kholia/Simple-TR-Switch/dual-channel-relay-2.jpg

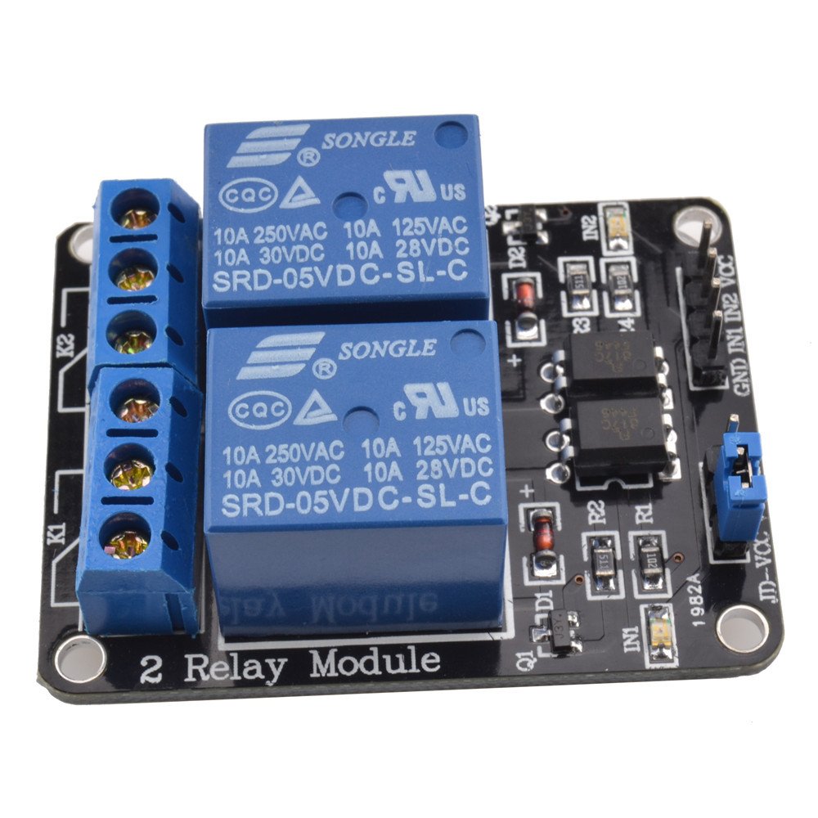
dual-channel-relay-2.jpg
