kholia/Simple-TR-Switch/Extender-PCB-1.png

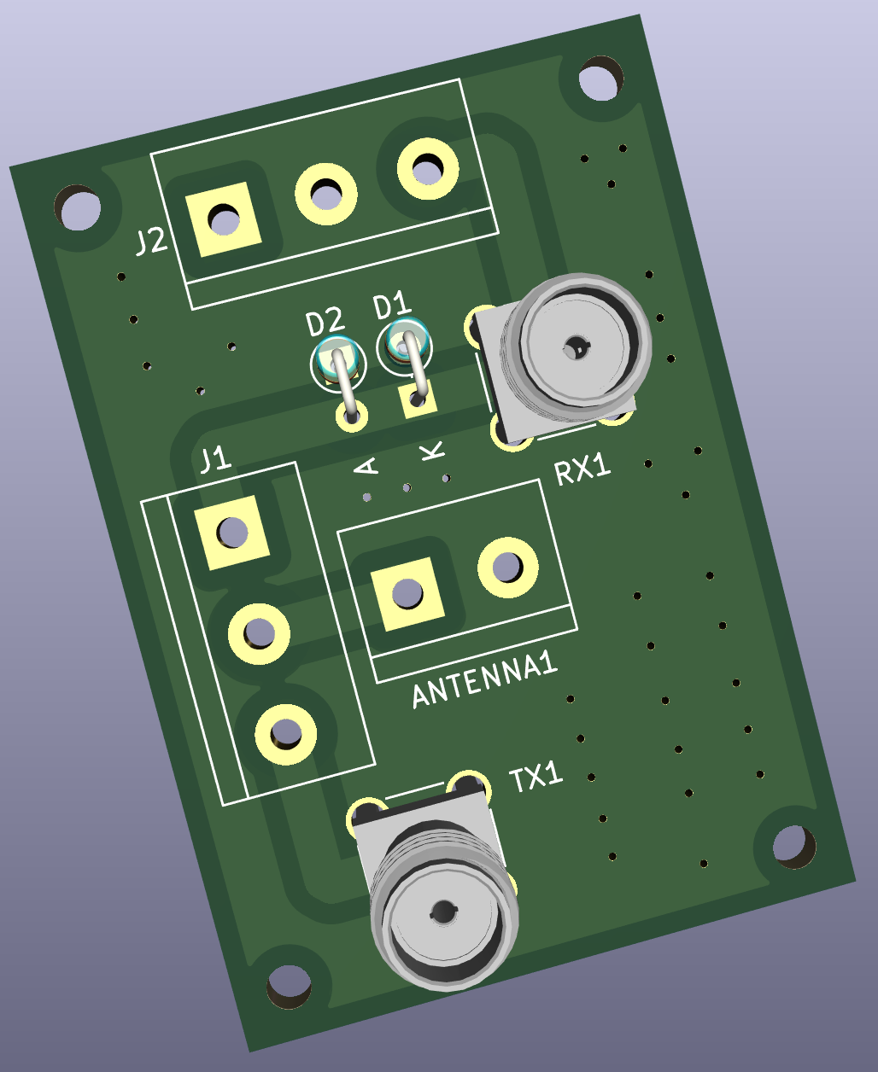
Extender-PCB-1.png
