kholia/Simple-TR-Switch/info/Optocoupler + NPN.png

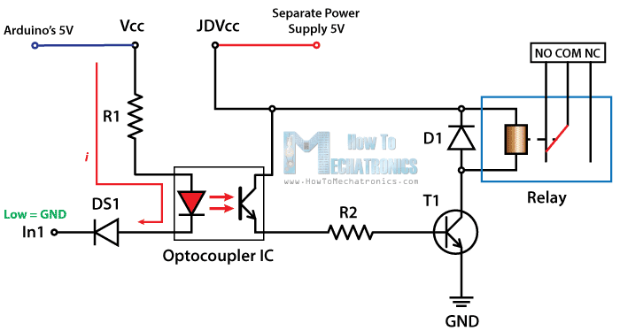
info/Optocoupler + NPN.png
