kholia/Simple-TR-Switch/info/Optocoupler-Relay-Driver-with-PC817-2N3904.jpg

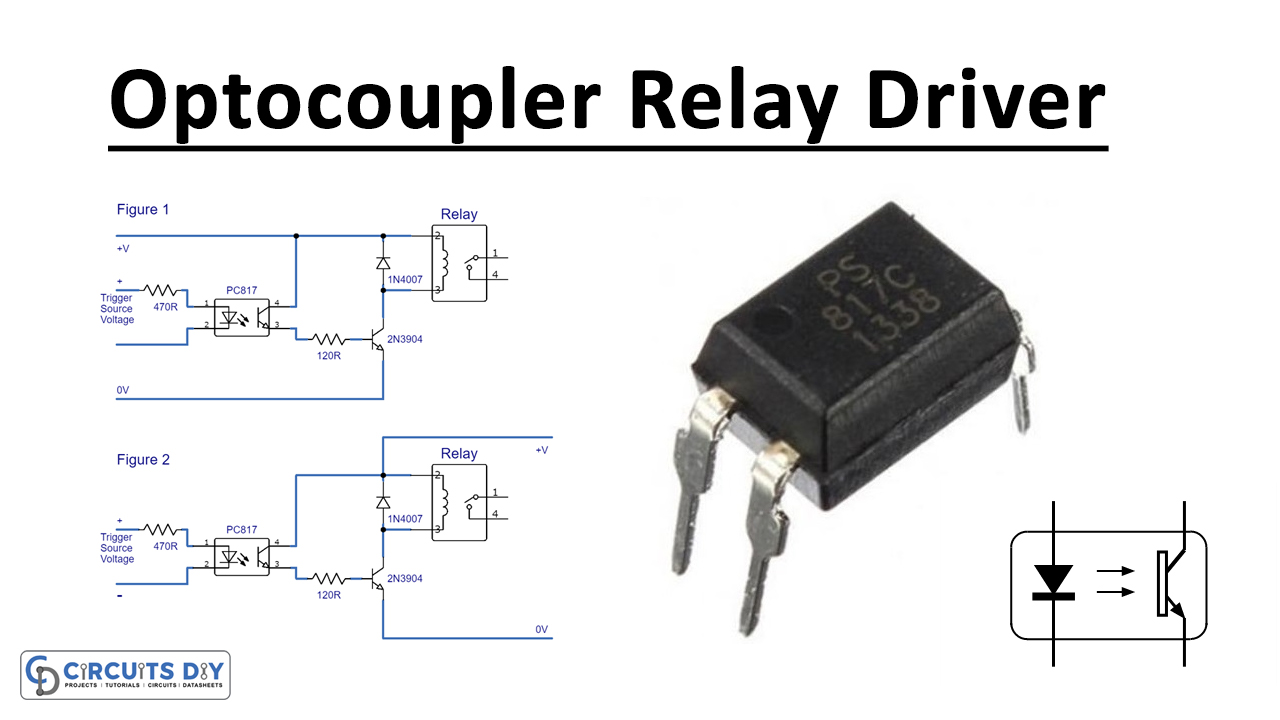
info/Optocoupler-Relay-Driver-with-PC817-2N3904.jpg
