kholia/Simple-TR-Switch/info/Optocoupler-With-Relay.png

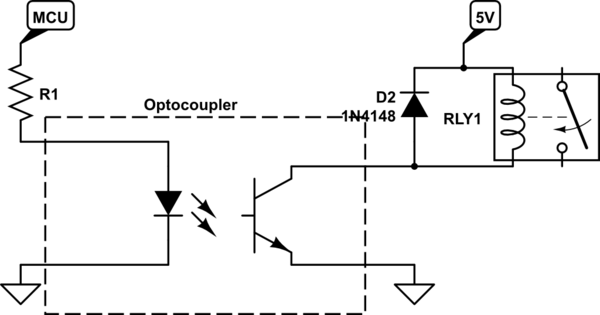
info/Optocoupler-With-Relay.png
