kholia/Simple-TR-Switch/PCB-Rendering-v3.png

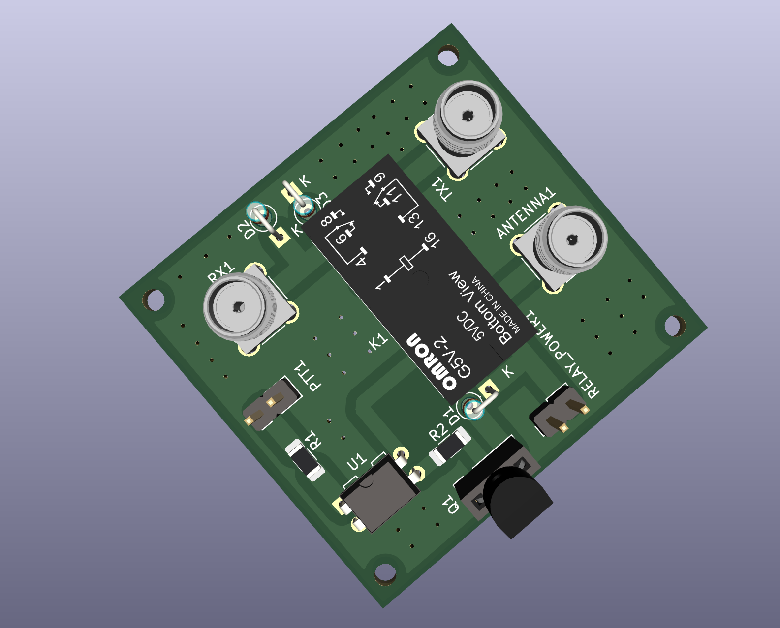
PCB-Rendering-v3.png
